keeeal/seacal-scanner/src/cad/scanner/platform/base-motor.scad

use <../../utils/motors/nema17.scad>

module base_motor() nema17_short();
