keeeal/seacal-scanner/src/cad/scanner/frame/arm/axle-screw.scad

module axle_screw() intersection()
{
    scale(0.5) import("../../../assets/axle-screw.stl");
    cylinder(18, r = 20);
}
