keeeal/seacal-scanner/src/cad/scanner/frame/arm/gopro-nut-and-bolt/gopro-bolt.scad

module gopro_bolt() import("../../../../assets/gopro-bolt/gopro-bolt.stl");
