keeeal/seacal-scanner/src/cad/scanner/frame/arm/gopro-nut-and-bolt/gopro-knob.scad

module gopro_knob() import("../../../../assets/gopro-bolt/gopro-knob.stl");
