keeeal/seacal-scanner/src/cad/scanner/frame/arm/gopro-nut-and-bolt/gopro-nut.scad

module gopro_nut() import("../../../../assets/gopro-bolt/gopro-nut.stl");
