keeeal/seacal-scanner/src/cad/scanner/frame/arm/phone-clamp/clamp-a.scad

module clamp_a() import("../../../../assets/phone-clamp/clamp-a.stl");
