keeeal/seacal-scanner/src/cad/scanner/frame/arm/phone-clamp/clamp-b.scad

module clamp_b() import("../../../../assets/phone-clamp/clamp-b.stl");
