keeeal/seacal-scanner/src/cad/scanner/frame/arm/phone-clamp/clamp-bolt.scad

module clamp_bolt() import("../../../../assets/phone-clamp/clamp-bolt.stl");
