keeeal/seacal-scanner/src/cad/scanner/frame/arm/phone-clamp/clamp-extender.scad

module clamp_extender() translate([ 0, 0, -7.5 ]) import("../../../../assets/phone-clamp/clamp-extender.stl");
