keeeal/seacal-scanner/src/cad/scanner/frame/arm/phone-clamp/clamp-knob.scad

module clamp_knob() import("../../../../assets/phone-clamp/clamp-knob.stl");
