keeeal/seacal-scanner/src/cad/scanner/frame/arm/phone-clamp/clamp-nut.scad

module clamp_nut() import("../../../../assets/phone-clamp/clamp-nut.stl");
