keeeal/seacal-scanner/src/cad/scanner/frame/arm/phone-clamp/clamp-screw.scad

module clamp_screw() import("../../../../assets/phone-clamp/clamp-screw.stl");
