keeeal/seacal-scanner/src/cad/scanner/platform/__subassembly__.scad

use <base-motor.scad>
use <platform-base/__subassembly__.scad>
use <bearing.scad>
use <motor-gear.scad>
use <platform-gear.scad>
use <platform-top.scad>

module platform()
{
    translate([ 0, 0, 60 ]) color([ 0.8, 0.8, 0.8 ]) bearing();
    // translate([0, 0, 54]) platform_gear();
    translate([ 91, 0, 43 ]) rotate([ 180, 0, 0 ]) base_motor();
    // translate([91, 0, 64]) rotate([180, 0, 0]) motor_gear();
    platform_base();
    translate([ 0, 0, 61 ]) platform_top();
}
